brandonbraun653/GPIODriver/Software/src/io_resources.hpp

/********************************************************************************
 *   File Name:
 *       io_resources.hpp
 *
 *   Description:
 *       Provides commonly used resources for interacting with the command line
 *       interface for the GPIODriver.
 *
 *   2019 | Brandon Braun | brandonbraun653@gmail.com
 ********************************************************************************/

#pragma once
#ifndef GPIO_DRIVER_IO_RESOURCES_HPP
#define GPIO_DRIVER_IO_RESOURCES_HPP

/* C++ Includes */
#include <string>

namespace GPIODriver::CommandLine
{
//  static constexpr std::string_view help_message = "lkjfs"
//                                                   "lksjdkf";
//
//  namespace Args
//  {
//    /*-------------------------------------------------
//    Argument options that can be parsed with cxxopts
//    -------------------------------------------------*/
//    static constexpr char delimiter = ' ';
//
//    static constexpr std::string_view help_short = "-h";
//    static constexpr std::string_view help_long = "--help";
//
//    static constexpr std::string_view enable_pin_short = "e";
//    static constexpr std::string_view enable_pin_long = "enable";
//    static constexpr std::string_view enable_pin_short_long = "e,enable";
//    
//    static constexpr std::string_view disable_pin_short = "-d";
//    static constexpr std::string_view disable_pin_long = "--disable";
//
//    static constexpr std::string_view read_pin_short = "-r";
//    static constexpr std::string_view read_pin_long = "--read";
//  } 
}

#endif /* !GPIO_DRIVER_IO_RESOURCES_HPP */
