brandonbraun653/GPIODriver/Software/src/thread_command_parser.cpp

/********************************************************************************
*   File Name:
*       
*
*   Description:
*       
*
*   2019 | Brandon Braun | brandonbraun653@gmail.com
********************************************************************************/

/* Chimera Includes */
#include <Chimera/chimera.hpp>
#include <Chimera/threading.hpp>

/* Command Line Parser Includes */
//#include <cxxopts.hpp>

/* Project Includes */
#include <io_resources.hpp>
