brandonbraun653/GPIODriver/Software/src/command_parser.cpp

/********************************************************************************
 *   File Name:
 *      command_parser.cpp
 *
 *   Description:
 *      Implements the command parser
 *
 *   2019 | Brandon Braun | brandonbraun653@gmail.com
 ********************************************************************************/


/* GPIO Driver Includes */
#include "command_parser.hpp"

namespace GPIODriver
{
  CommandParser::CommandParser()
  {
  }

  CommandParser::~CommandParser()
  {
  }

  void CommandParser::somefunc()
  {
  }
}  // namespace GPIODriver
